frankalicious/room-board/firmware/msp430-gcc/uart/uart.c

/*
 * This file is part of the MSP430 hardware UART example.
 *
 * Copyright (C) 2012 Stefan Wendler <sw@kaltpost.de>
 *
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
 * You should have received a copy of the GNU General Public License
 * along with this program.  If not, see <http://www.gnu.org/licenses/>.
 */

/******************************************************************************
 * Hardware UART example for MSP430.
 *
 * Stefan Wendler
 * sw@kaltpost.de
 * http://gpio.kaltpost.de
 ******************************************************************************/

#include <msp430.h>
#include <legacymsp430.h>

#include "uart.h"

/**
 * Receive Data (RXD) at P1.1
 */
#define RXD		BIT1

/**
 * Transmit Data (TXD) at P1.2
 */
#define TXD		BIT2

/**
 * Callback handler for receive
 */
void (*uart_rx_isr_ptr)(unsigned char c);
__interrupt void USCI0RX_ISR(void);

void uart_init(void)
{
	uart_set_rx_isr_ptr(0L);

	P1SEL  = RXD + TXD;                       
  	P1SEL2 = RXD + TXD;                       
  	UCA0CTL1 |= UCSSEL_2;                     /* SMCLK */
  	UCA0BR0 = 104;                            /* 1MHz 9600 */
  	UCA0BR1 = 0;                              /* 1MHz 9600 */
  	UCA0MCTL = UCBRS0;                        /* Modulation UCBRSx = 1 */
  	UCA0CTL1 &= ~UCSWRST;                     /* Initialize USCI state machine */
  	IE2 |= UCA0RXIE;                          /* Enable USCI_A0 RX interrupt */
}

void uart_set_rx_isr_ptr(void (*isr_ptr)(unsigned char c)) 
{
	uart_rx_isr_ptr = isr_ptr;	
}

unsigned char uart_getc()
{
    while (!(IFG2&UCA0RXIFG));                /* USCI_A0 RX buffer ready? */
	return UCA0RXBUF;
}

void uart_putc(unsigned char c)
{
	while (!(IFG2&UCA0TXIFG));              /* USCI_A0 TX buffer ready? */
  	UCA0TXBUF = c;                    		/* TX */
}

void uart_puts(const char *str)
{
     while(*str) uart_putc(*str++);
}

interrupt(USCIAB0RX_VECTOR) USCI0RX_ISR(void)
{
	if(uart_rx_isr_ptr != 0L) {
		(uart_rx_isr_ptr)(UCA0RXBUF);
	}
}
